atulloh/oddball/output/pcbs/v2.1/schematic.png

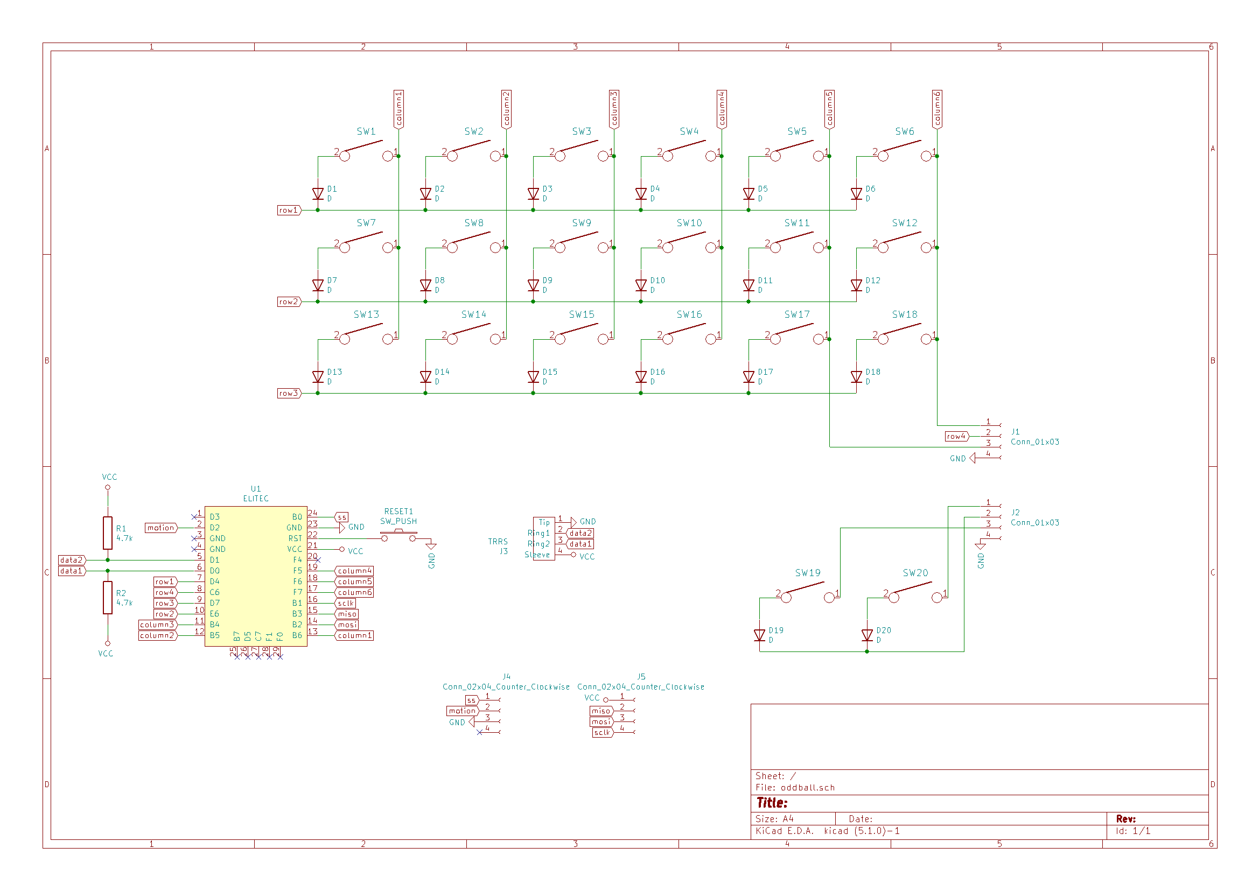
output/pcbs/v2.1/schematic.png
