atulloh/oddball/src/components/leftCase.scad

use <../modules/leftCase.scad>;

leftCase($fn = 100);
