atulloh/oddball/src/components/leftPlate.scad

include <../config.scad>;
use <../modules/pcb.scad>;
use <../modules/plate.scad>;
use <../modules/keys.scad>;

linear_extrude(PLATE_THICKNESS)
    plate(
        keyPositions = FINGER_GRID,
        keyHeight = 1.0,
        boltPositions = FINGER_BOLT_HOLES,
        cutHoles = true,
        $fn = 100);
    
if(DRAW_DEBUG){
    %keys(
        keyPositions = FINGER_GRID,
        keyHeight = 1.0,
        $fn = 20);

    %translate([0,0, -PCB_PLATE_OFFSET_Z - PCB_THICKNESS])
        linear_extrude(PCB_THICKNESS)
            pcb(
                keyPositions = FINGER_GRID,
                boltPositions = FINGER_BOLT_HOLES,
                keyHeight = 1.0,
                $fn = 20);
}
