atulloh/oddball/src/components/rightCase.scad

use <../modules/rightCase.scad>;

rightCase($fn = 100);
