atulloh/oddball/src/components/thumbPcb.scad

include<../config.scad>;
use<../modules/pcb.scad>;

pcb(
    THUMB_GRID,
    THUMB_BOLT_HOLES,
    1.25,
    $fn = 100);
