atulloh/oddball/src/modules/keycap.scad

use <shapes.scad>

// draws a rough no-profile at keycap 0,0 1U space
module keycap(keyHeight = 1.0){
  
    1U = 19.05;
    width = 18;
    depth = 18 * keyHeight;
    height = 9;

    translate([1U/2, 1U/2, 7])
        linear_extrude(height, scale = [0.7,0.7])
          squircle([width, depth], 1, center = true);	
}

keycap($fn = 100);
